eliddell1/Project-Blue-Fist/Images/device+app-targeted_attack_mode.jpg

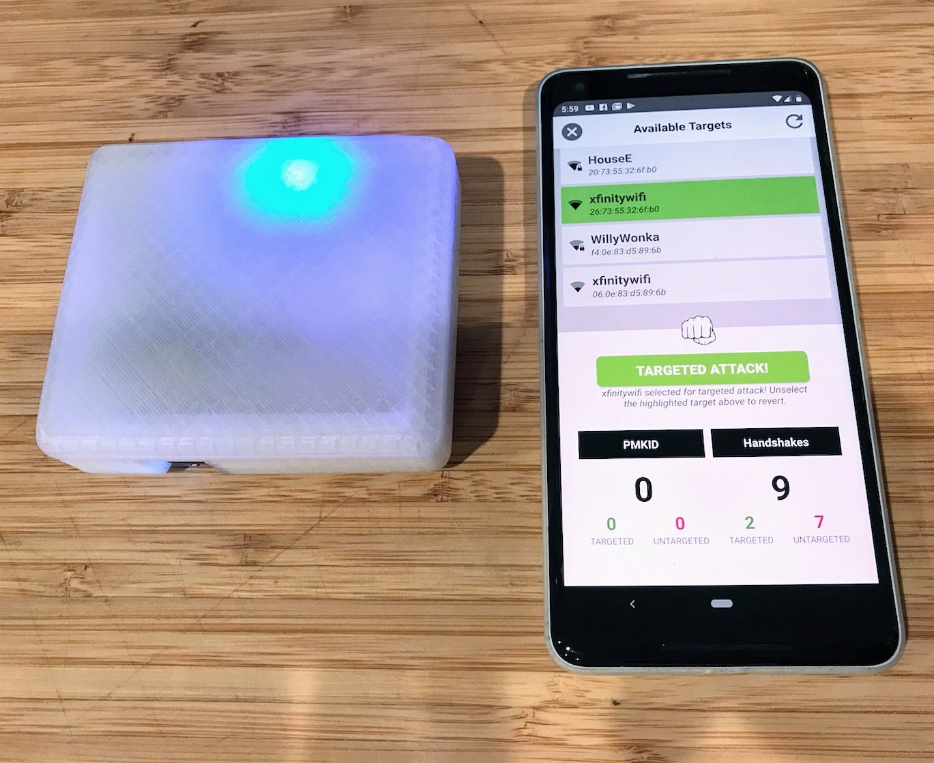
Images/device+app-targeted_attack_mode.jpg
