eliddell1/Project-Blue-Fist/Images/Screenshot_20181109-175958.png

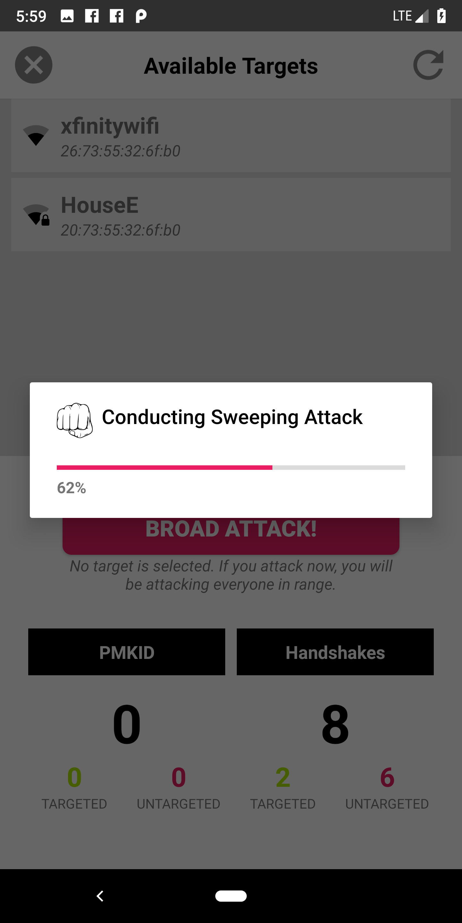
Images/Screenshot_20181109-175958.png
